trlafleur/Soil_Moisture_Sensor_MS_R1.1-RFM95/Doc/IMG_5178.JPG

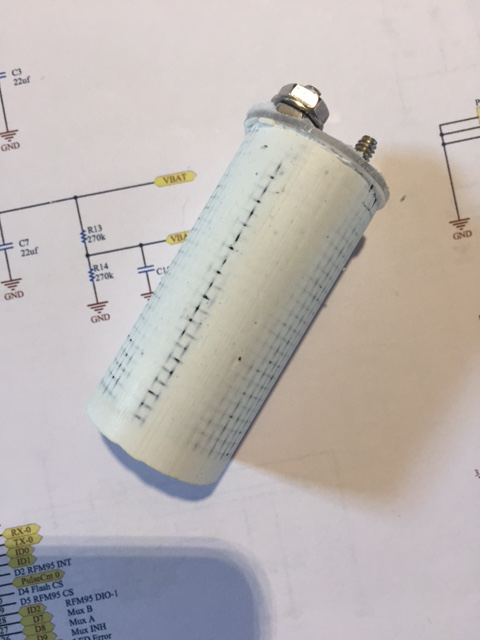
Doc/IMG_5178.JPG
